w4iei/PHOTON/firmware/src/core1/events.c

#include "core1/events.h"

#include <string.h>

photon_events_t g_events;

// Effective range floor scales with the OSR accumulation (170 << 3 = 1360).
#define MIN_EVENT_RANGE_SCALED ((uint32_t)PHOTON_MIN_EVENT_RANGE << PHOTON_OSR_MODE)

void events_init(uint32_t disabled_mask) {
    memset(&g_events, 0, sizeof g_events);
    g_events.disabled_mask = disabled_mask;
    for (int i = 0; i < PHOTON_MAX_SENSORS; i++) {
        g_events.min[i] = 0xFFFF;
        g_events.max[i] = 0;
    }
}

void events_seed_cal(uint8_t idx, uint16_t mn, uint16_t mx) {
    if (idx >= PHOTON_MAX_SENSORS) {
        return;
    }
    g_events.min[idx] = mn;
    g_events.max[idx] = mx;
}

// Clearing a sensor's state while its note is ON must emit the OFF first —
// otherwise a disable/cal-reset during a held key leaves the MIDI note stuck
// at the bridge forever. dt = 100 ms maps to the minimum release velocity.
static inline void clear_sensor_state(photon_events_t *e, int i) {
    if (e->note_on[i]) {
        event_ring_push((uint8_t)i, 0, 100000u, e->last_now_us);
    }
    e->note_on[i] = false;
    e->strike_pending[i] = false;
    e->release_pending[i] = false;
}

void events_reset_cal(void) {
    for (int i = 0; i < PHOTON_MAX_SENSORS; i++) {
        g_events.min[i] = 0xFFFF;
        g_events.max[i] = 0;
        clear_sensor_state(&g_events, i);
    }
}

void events_process(const uint16_t *readings, uint32_t now_us) {
    photon_events_t *e = &g_events;
    e->last_now_us = now_us;

    for (int i = 0; i < PHOTON_ACTIVE_SENSORS; i++) {
        if ((e->disabled_mask >> i) & 1u) {
            e->value[i] = 0;
            clear_sensor_state(e, i);
            continue;
        }
        uint16_t v = readings[i];
        e->value[i] = v;
        if (v == 0) {
            continue;  // dead read; never calibrate on it
        }
        // Rolling noise stats (EMA window ~64 sweeps).
        if (e->mean_fp6[i] == 0) {
            e->mean_fp6[i] = (uint32_t)v << 6;
        }
        e->mean_fp6[i] += (uint32_t)(((int32_t)((uint32_t)v << 6) -
                                      (int32_t)e->mean_fp6[i]) >> 6);
        int32_t dev = (int32_t)v - (int32_t)(e->mean_fp6[i] >> 6);
        e->var_ema[i] += (uint32_t)(((dev * dev) - (int32_t)e->var_ema[i]) >> 6);
        if (e->learning) {
            if (v < e->min[i]) {
                e->min[i] = v;
            }
            if (v > e->max[i]) {
                e->max[i] = v;
            }
        }
        uint32_t mn = e->min[i], mx = e->max[i];
        if (mx <= mn) {
            // Uncalibrated (min still 0xFFFF) or degenerate: inactive.
            // Guards the frozen-empty case from an unsigned underflow that
            // would otherwise fabricate a huge range.
            clear_sensor_state(e, i);
            continue;
        }
        uint32_t rng = mx - mn;
        if (rng < MIN_EVENT_RANGE_SCALED) {
            clear_sensor_state(e, i);
            continue;
        }

        // Threshold ladder (integer, percent of range). "Up" direction =
        // key press for normal polarity; inverted sensors mirror around max.
        uint32_t vel_start_pct = PHOTON_STRIKE_PCT > PHOTON_STRIKE_WINDOW_PCT
                                     ? (uint32_t)(PHOTON_STRIKE_PCT - PHOTON_STRIKE_WINDOW_PCT)
                                     : 0;                                     // 30
        uint32_t rel_vel_pct = PHOTON_STRIKE_PCT + PHOTON_VELOCITY_WINDOW_PCT; // 80
        if (rel_vel_pct > 100) {
            rel_vel_pct = 100;
        }
        uint32_t rel_pct = PHOTON_RELEASE_PCT < PHOTON_STRIKE_PCT
                               ? PHOTON_RELEASE_PCT
                               : PHOTON_STRIKE_PCT;                            // 40

        // How far into the range the key currently is, clamped to 0..rng.
        // The clamp matters with frozen calibration: thermal/duty drift can
        // move the idle level BELOW the stored min (or above max, inverted),
        // and an unsigned underflow here read as a full-scale press.
        uint32_t press;
        if ((e->polarity_mask >> i) & 1u) {
            press = v < mx ? mx - v : 0;
        } else {
            press = v > mn ? v - mn : 0;
        }
        if (press > rng) {
            press = rng;
        }
        uint32_t vel_start_thr = rng * vel_start_pct / 100;
        uint32_t strike_thr = rng * PHOTON_STRIKE_PCT / 100;
        uint32_t rel_vel_thr = rng * rel_vel_pct / 100;
        uint32_t rel_thr = rng * rel_pct / 100;

        if (!e->note_on[i]) {
            // Strike: arm on crossing the velocity-start threshold, fire ON
            // at the strike threshold; dt = time between the two crossings.
            // (A jump past both thresholds in one sweep arms and fires in
            // the same iteration — dt 0, the fastest measurable strike.)
            if (!e->strike_pending[i] && press >= vel_start_thr) {
                e->strike_pending[i] = true;
                e->strike_t_us[i] = now_us;
            }
            if (e->strike_pending[i]) {
                if (press >= strike_thr) {
                    uint32_t dt = now_us - e->strike_t_us[i];
                    e->note_on[i] = true;
                    e->strike_pending[i] = false;
                    e->release_pending[i] = false;
                    e->events_on++;
                    event_ring_push((uint8_t)i, 1, dt, now_us);
                } else if (press < vel_start_thr) {
                    e->strike_pending[i] = false;  // disarm: retreated
                }
            }
        } else {
            // Release: symmetric, coming down through the release-velocity
            // threshold then the release threshold.
            if (!e->release_pending[i]) {
                if (press <= rel_vel_thr) {
                    e->release_pending[i] = true;
                    e->release_t_us[i] = now_us;
                }
            }
            if (e->release_pending[i]) {
                if (press <= rel_thr) {
                    uint32_t dt = now_us - e->release_t_us[i];
                    e->note_on[i] = false;
                    e->release_pending[i] = false;
                    e->events_off++;
                    event_ring_push((uint8_t)i, 0, dt, now_us);
                } else if (press > rel_vel_thr) {
                    e->release_pending[i] = false;  // disarm: went back up
                }
            }
        }
    }
}
